sacarlson/FreeCAD_examples/pcp_air_gun_design/viewable_stl_files/pcp_airtank-BodyPocket.stl

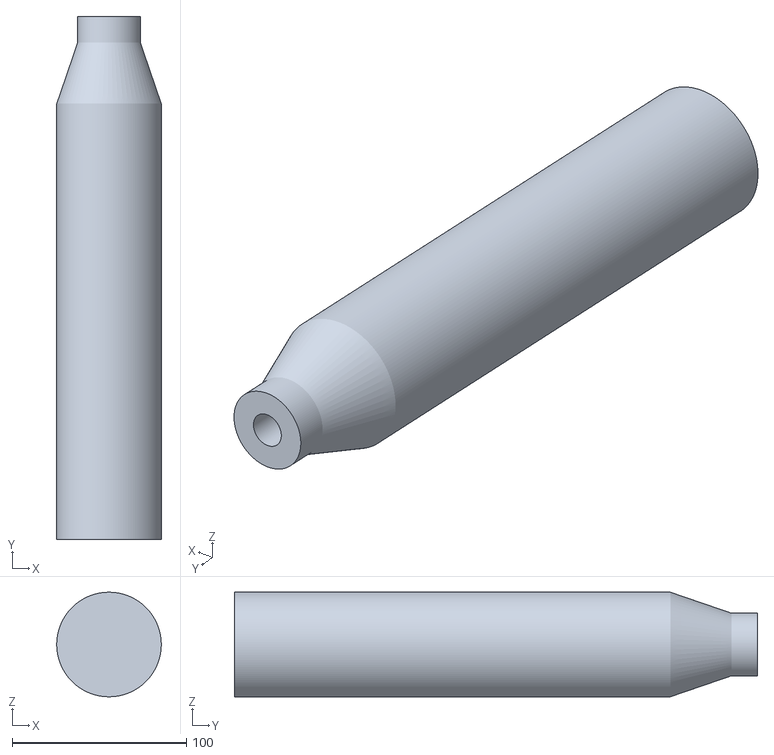
[picture p12: CAD file, 2025-09-18]
pcp_air_gun_design/viewable_stl_files/pcp_airtank-BodyPocket.stl
60.0 x 300.0 x 60.0
