sacarlson/FreeCAD_examples/pcp_air_gun_design/pcp_barel_14x3x596mm_8mmid.FCStd

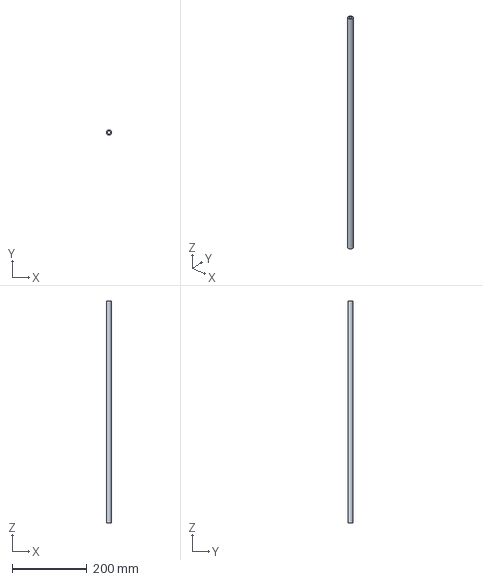
[picture p13: CAD file, 2025-09-18]
pcp_air_gun_design/pcp_barel_14x3x596mm_8mmid.FCStd
14.0 x 14.0 x 596.0 mm
